leoo-c1/Guitar-Synthesizer/electronics/simulation/Board_Power.asc

C1: cap; 10µ
C2: cap; 1µ
C3: cap; .1µ
C4: cap; 22µ; V=6.3 Irms=0 Rser=0.005 Lser=0
C5: cap; 4.7p
C6: cap; 2.2µ
C7: cap; 10µ
D1: diode; P6SMB20A
D2: diode; B160
D3: diode; B160
L1: ind; 4.7µ; Ipk=2.1 Rser=25m
R1: res; 20K
R2: res; 1Meg
R3: res; 191k
R4: res; 4.17
U1: LT8619
U2: LT1963A-3.3
V1: voltage; 9
Named nets: 0, OUT, IN
.model P6SMB20A D(Is=147.56E-18 N=1.0123 Rs=.395 Ikf=.16958 Cjo=13.986E-12 M=.3554 Vj=.80787 Isr=35.079E-12 Bv=19 Ibv=5.0000E-3 Tt=266.90E-9 Nbv=0.3 Tbv1=0.00073 Vpk=27.7 mfg=Littelfuse type=Zener)
.lib B160.LIB
.tran 0 2m 0.4m
