leoo-c1/Guitar-Synthesizer/electronics/simulation/Clamping_Test.asc

C1: cap; 4.7n
C2: cap; 0.47n
C3: cap; 4.7n
C4: cap; 1n
C5: cap; 100n
C6: cap; 1n
D1: diode; BAS116
D2: diode; BAS116
R1: res; 68.1k
R2: res; 1.15k
R3: res; 14.7k
R4: res; 2.52k
R5: res; 2Meg
R6: res; 100
R7: res; 10k
R8: res; 15.2k
R9: res; 1.13k
R10: res; 680
R11: res; 2Meg
U1: UniversalOpAmp
U2: UniversalOpAmp
V1: voltage; 3.3
V2: voltage; 3.3
V3: voltage; 1.65
V4: voltage; 1.65
V5: voltage; 1.65
V6: voltage; 3.3
V_in1: voltage; SINE(0 5 100)
Named nets: 0, V_out
.tran 0 50m 0 startup
.lib BAS116.LIB
